marcelomaximiano/BoardGame/boardgame.jpg

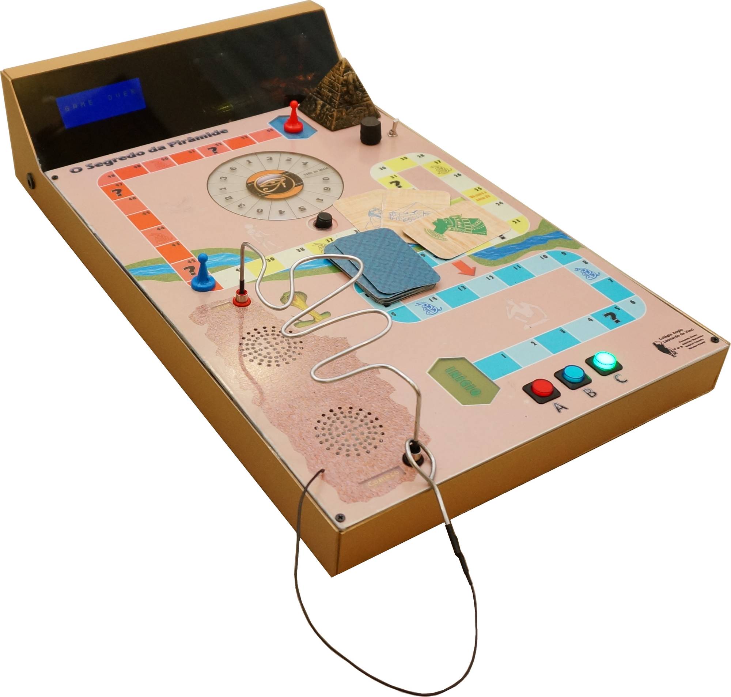
boardgame.jpg
