marcelomaximiano/BoardGame/hardware/BoardGame_pcb.png

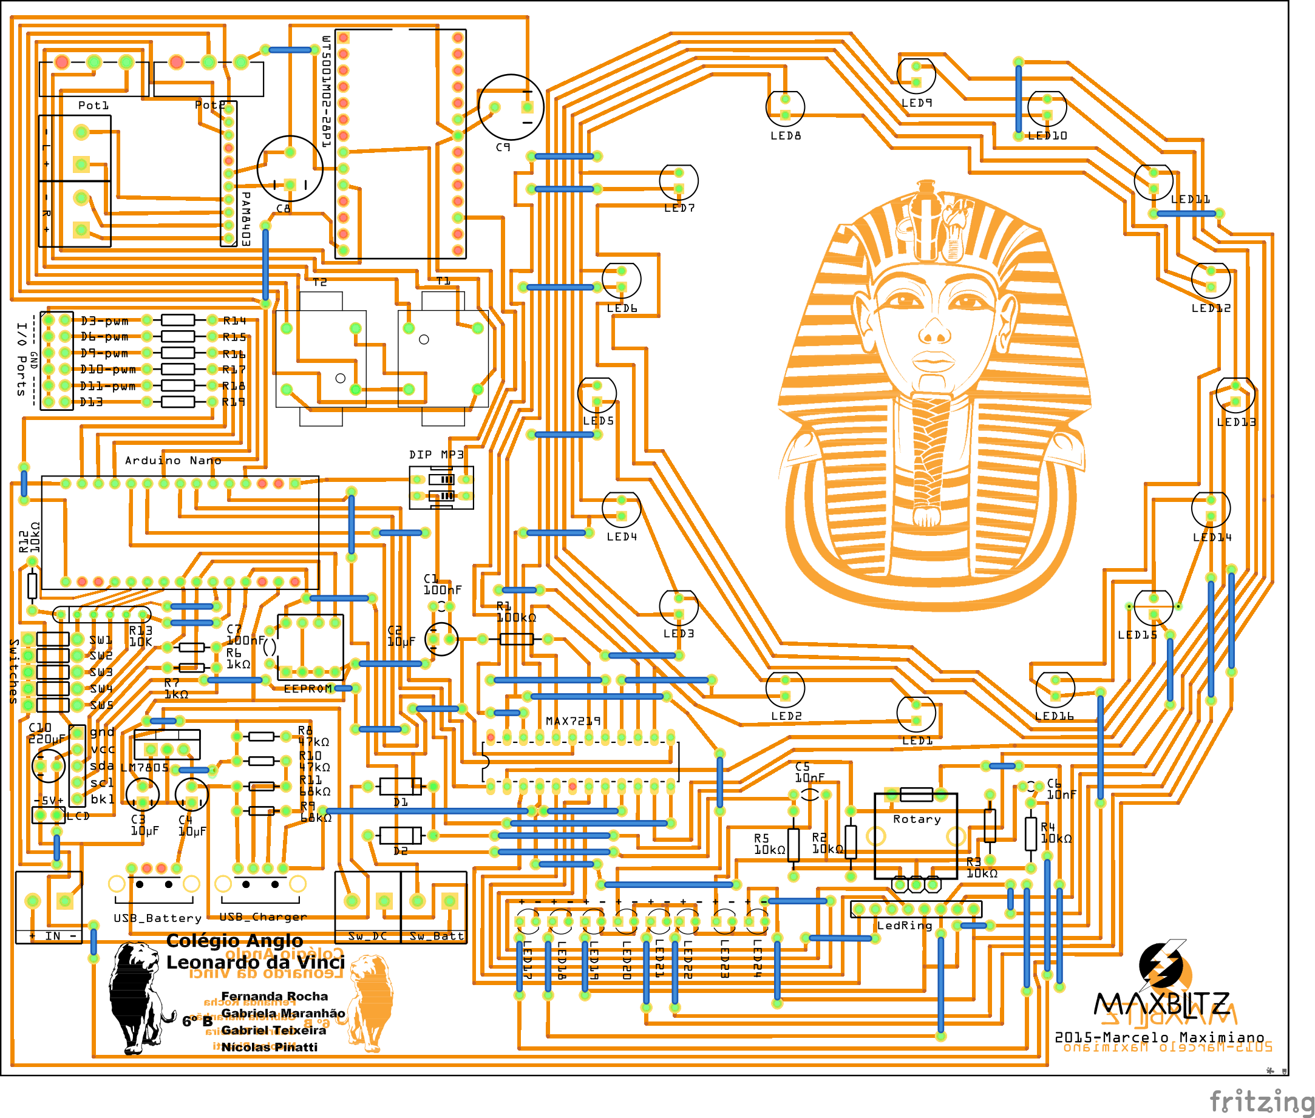
hardware/BoardGame_pcb.png
