marcelomaximiano/BoardGame/pictures/01-Board_sketch.jpg

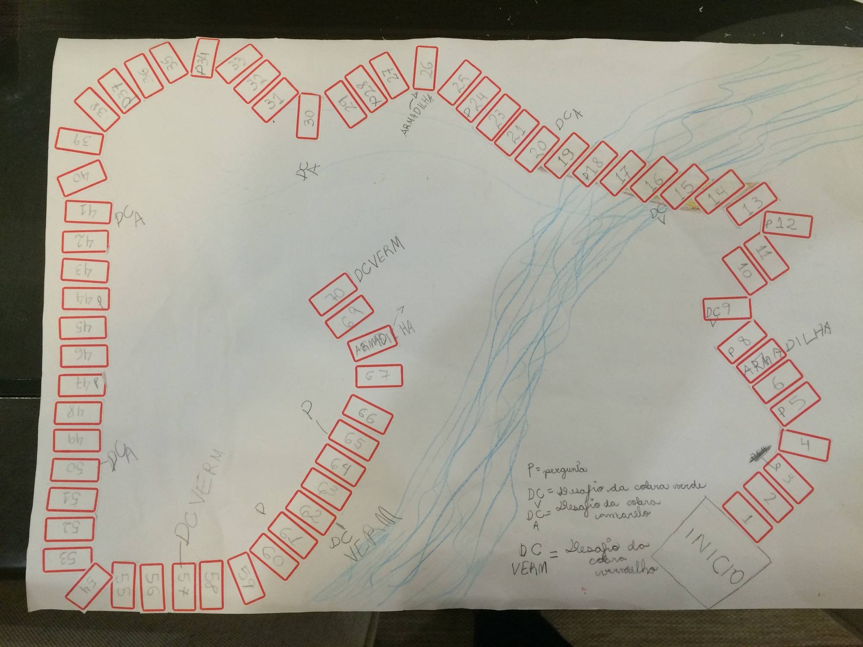
pictures/01-Board_sketch.jpg
