marcelomaximiano/BoardGame/pictures/02-First_Prototype.jpg

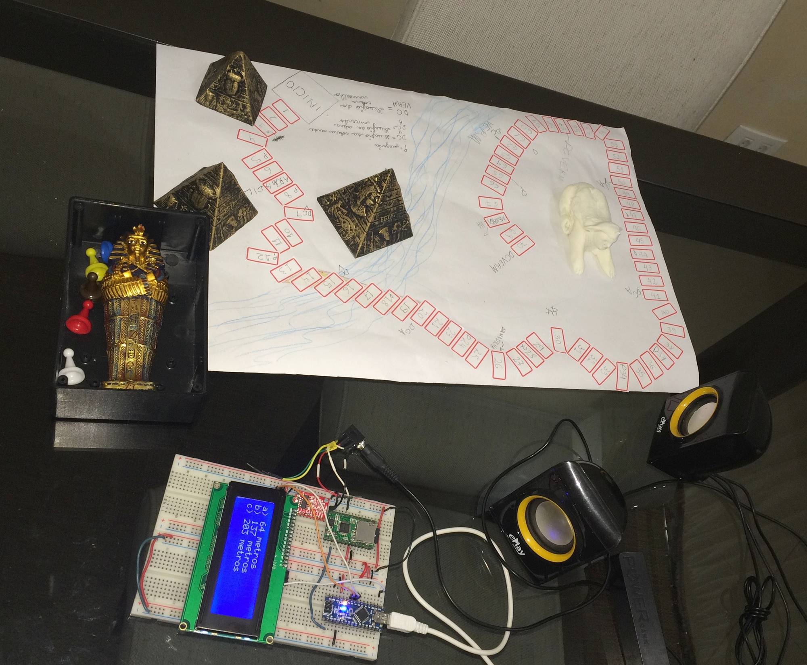
pictures/02-First_Prototype.jpg
