marcelomaximiano/BoardGame/pictures/03-PCB_tone_transfer.jpg

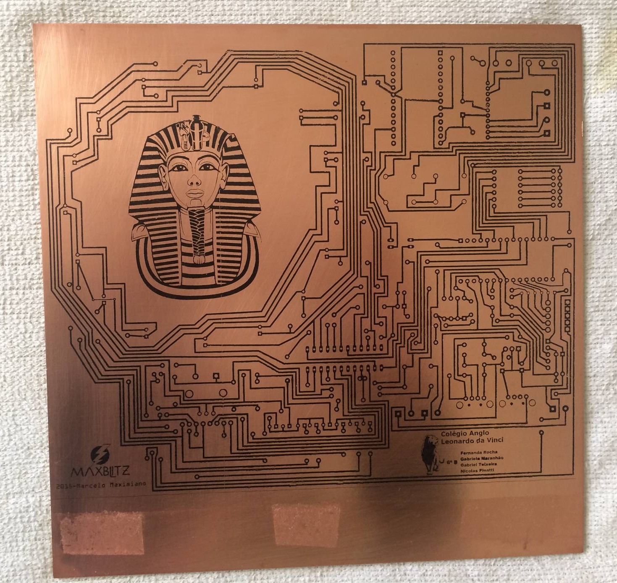
pictures/03-PCB_tone_transfer.jpg
