marcelomaximiano/BoardGame/pictures/04-PCB_Etched.jpg

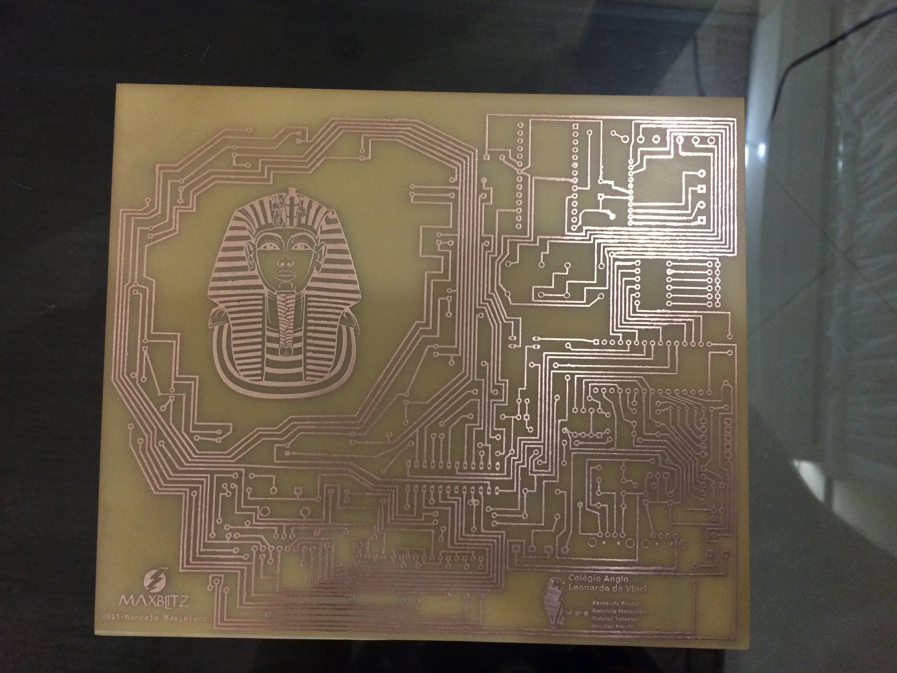
pictures/04-PCB_Etched.jpg
