marcelomaximiano/BoardGame/pictures/08-PCB_ready.jpg

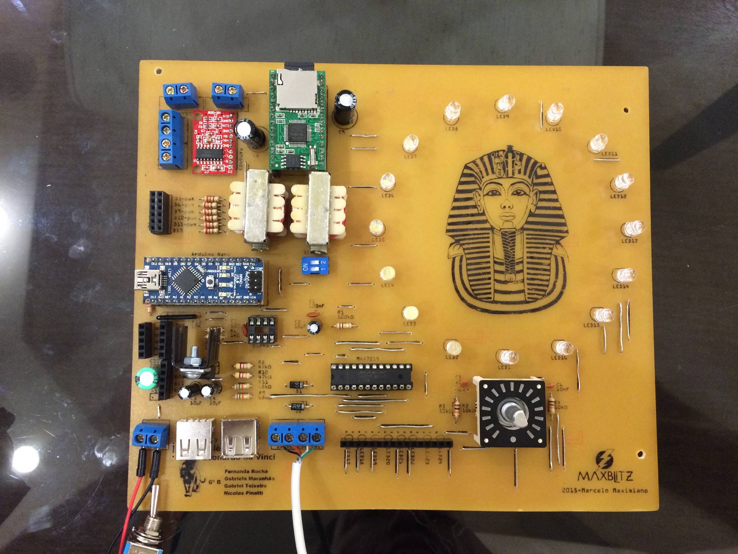
pictures/08-PCB_ready.jpg
