marcelomaximiano/BoardGame/pictures/12-Enclosure_cutting.jpg

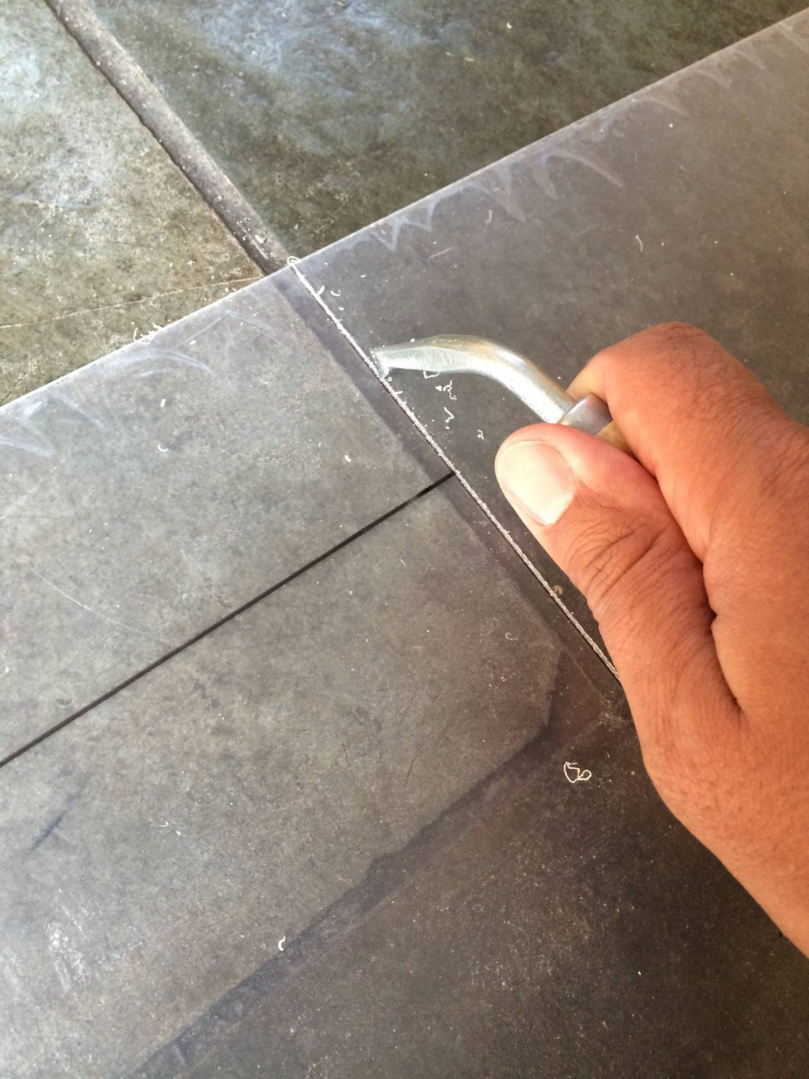
pictures/12-Enclosure_cutting.jpg
