marcelomaximiano/BoardGame/pictures/13-Enclosure_glueing.jpg

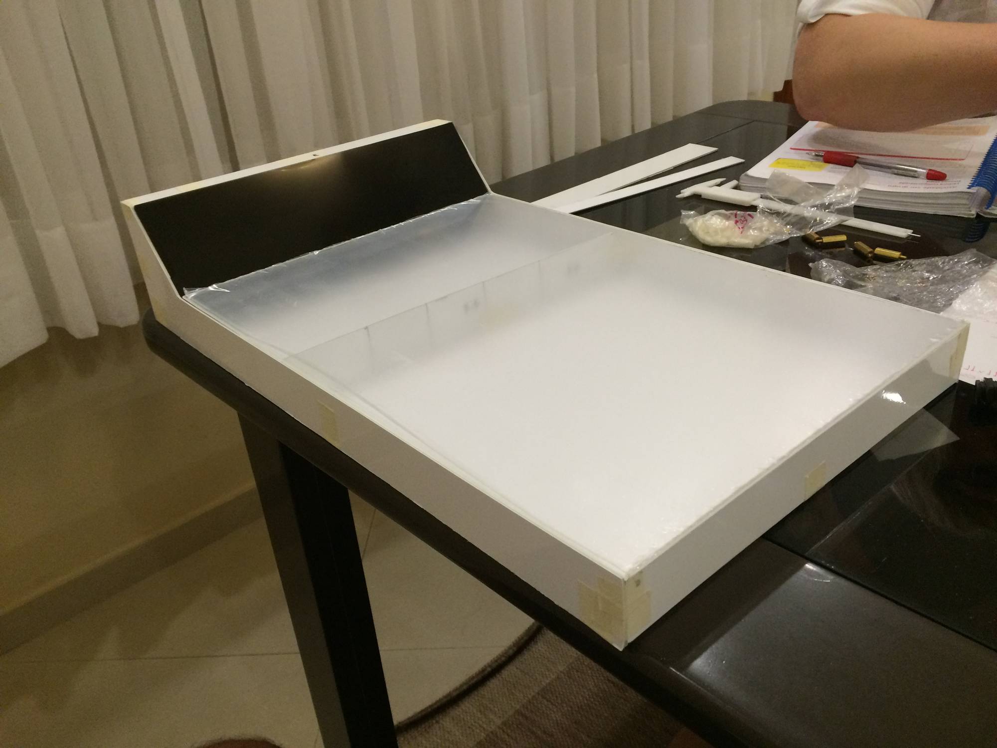
pictures/13-Enclosure_glueing.jpg
