marcelomaximiano/BoardGame/pictures/14-Enclosure_paint_prepation.jpg

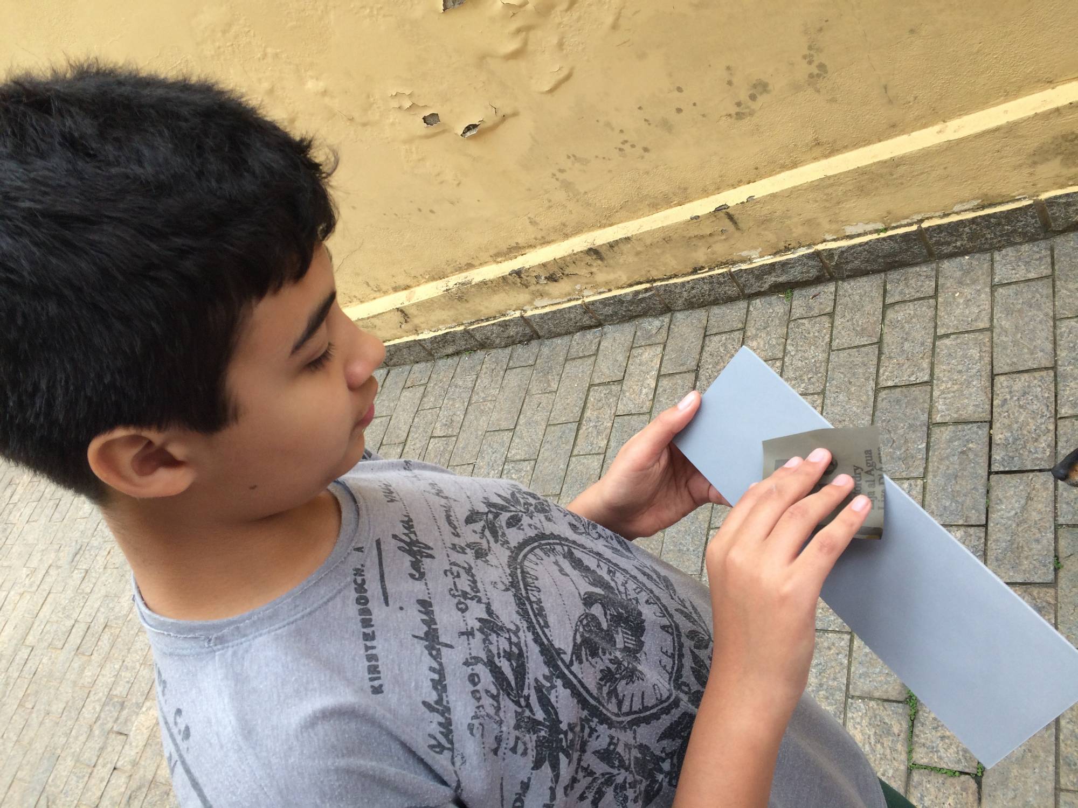
pictures/14-Enclosure_paint_prepation.jpg
