marcelomaximiano/BoardGame/pictures/15-Enclosure_paint_preparation2.jpg

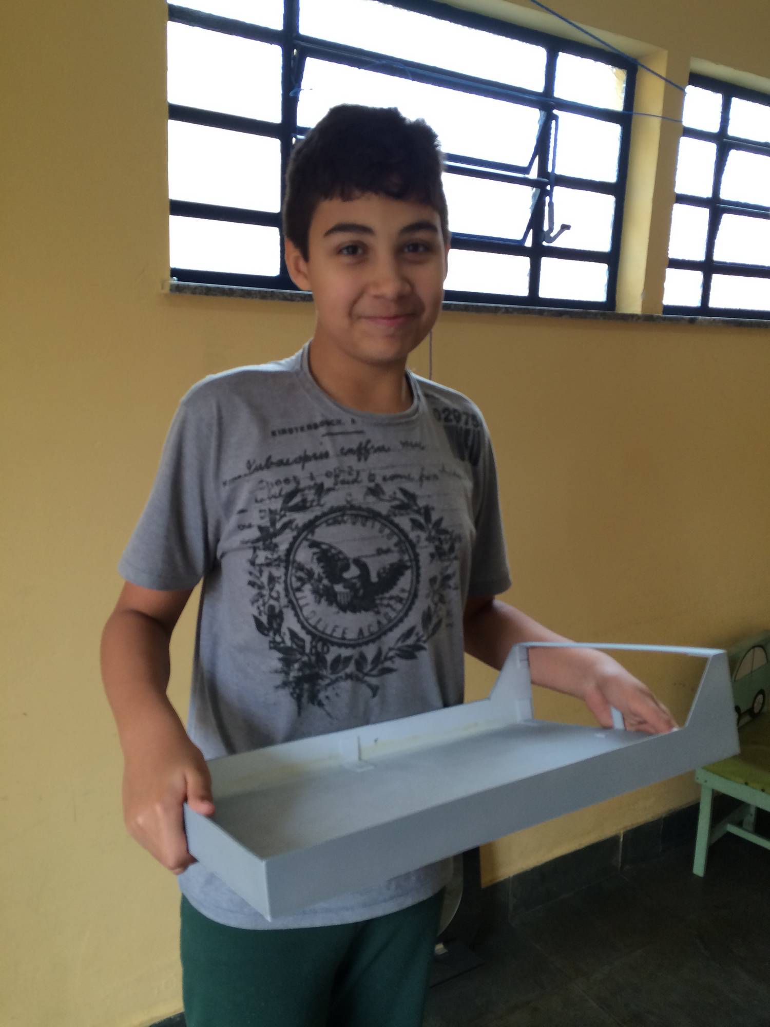
pictures/15-Enclosure_paint_preparation2.jpg
