marcelomaximiano/BoardGame/pictures/16-Enclosure_painting.jpg

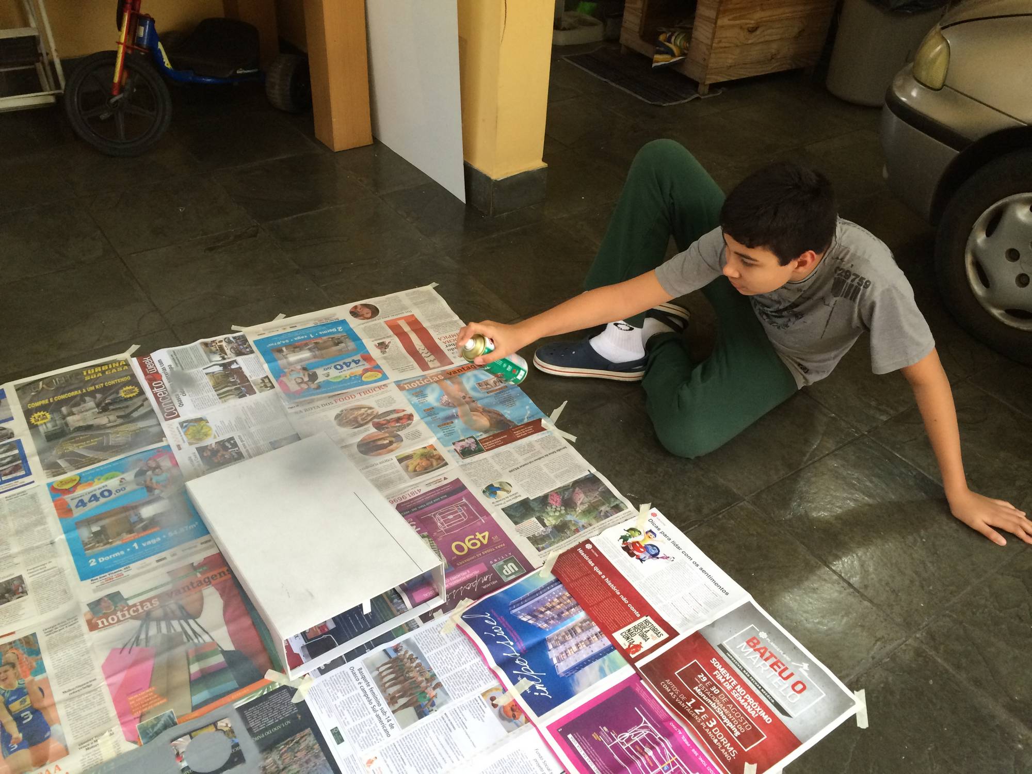
pictures/16-Enclosure_painting.jpg
