marcelomaximiano/BoardGame/pictures/18-Voice_recording.jpg

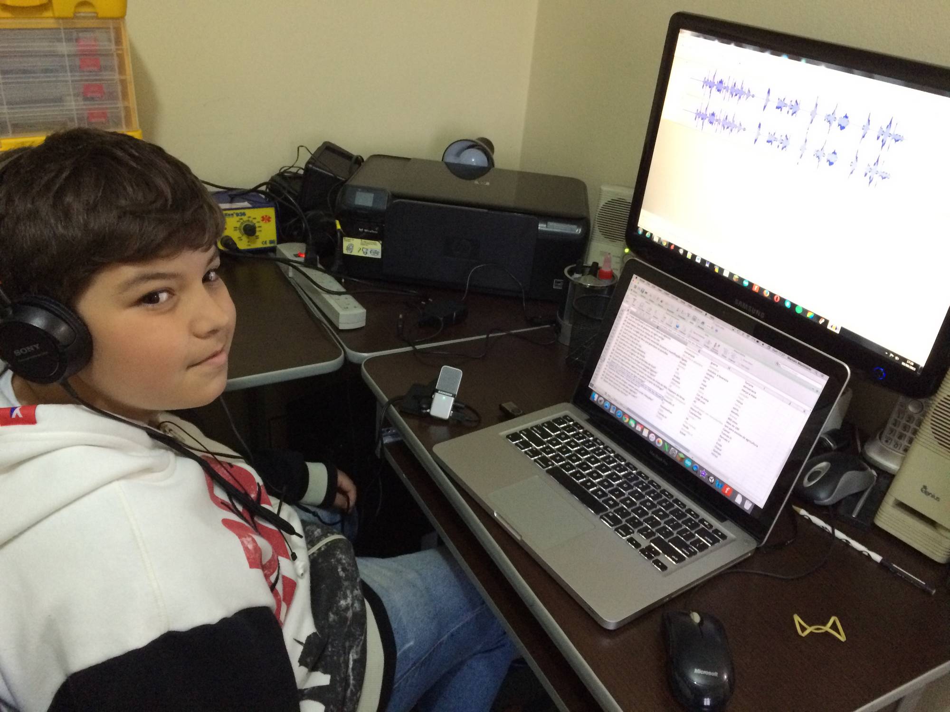
pictures/18-Voice_recording.jpg
