marcelomaximiano/BoardGame/pictures/20-RedPlayerWon_Secret_Revealed.jpg

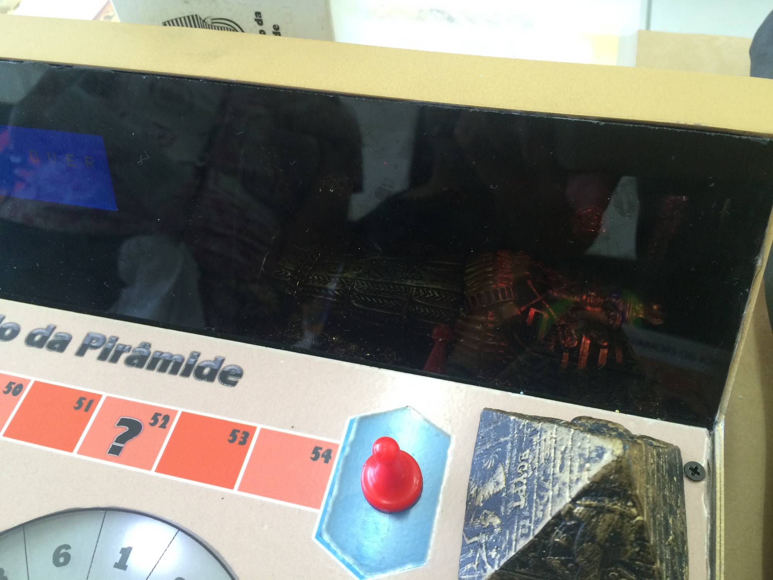
pictures/20-RedPlayerWon_Secret_Revealed.jpg
