marcelomaximiano/BoardGame/pictures/21-Pharaoh_Revealed.jpg

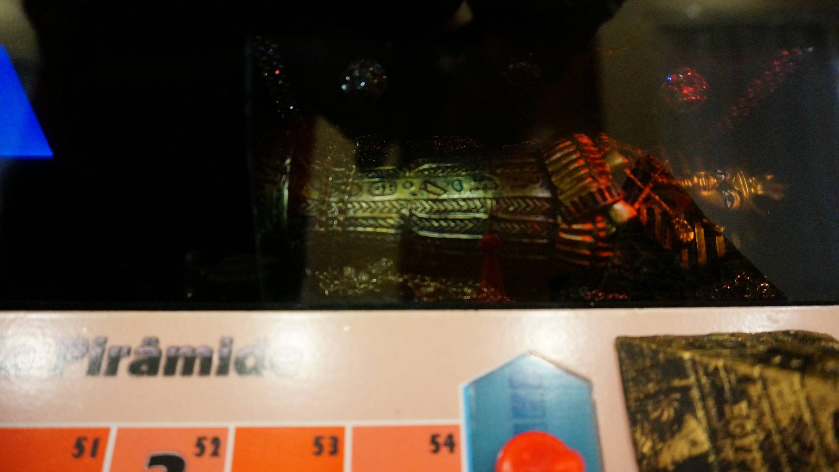
pictures/21-Pharaoh_Revealed.jpg
