marcelomaximiano/BoardGame/pictures/06-Nick_Soldering2.jpg

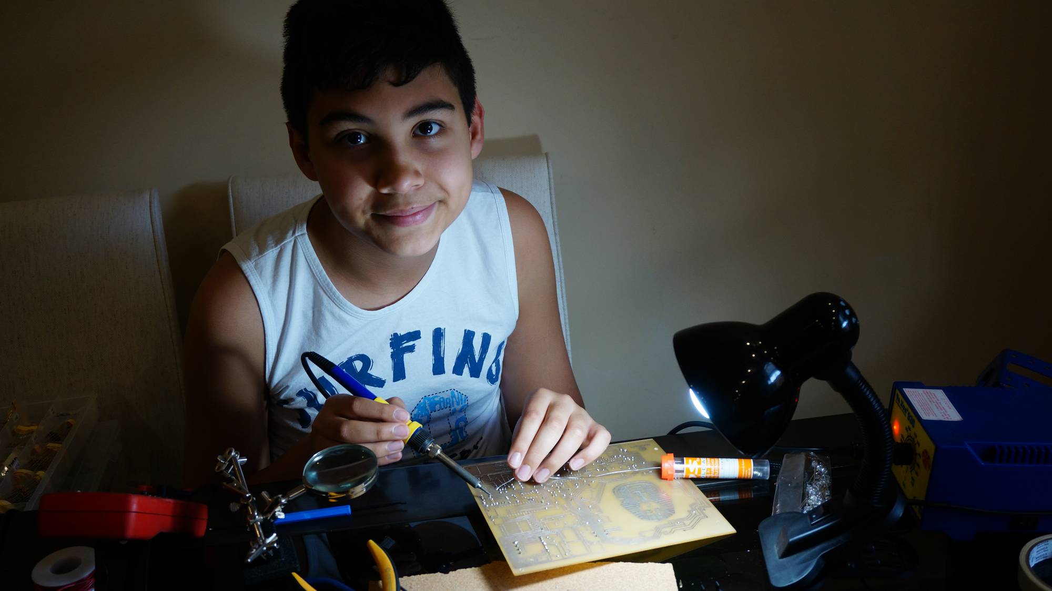
pictures/06-Nick_Soldering2.jpg
