marcelomaximiano/BoardGame/pictures/07-PCB-Soldered.jpg

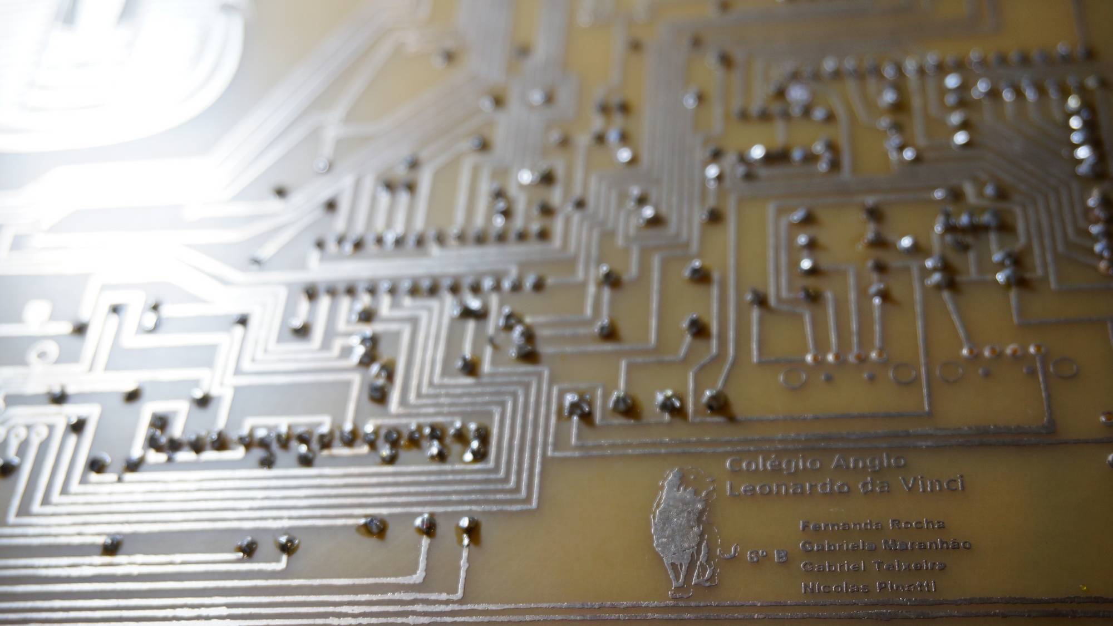
pictures/07-PCB-Soldered.jpg
