marcelomaximiano/BoardGame/pictures/09-PCB_testing.jpg

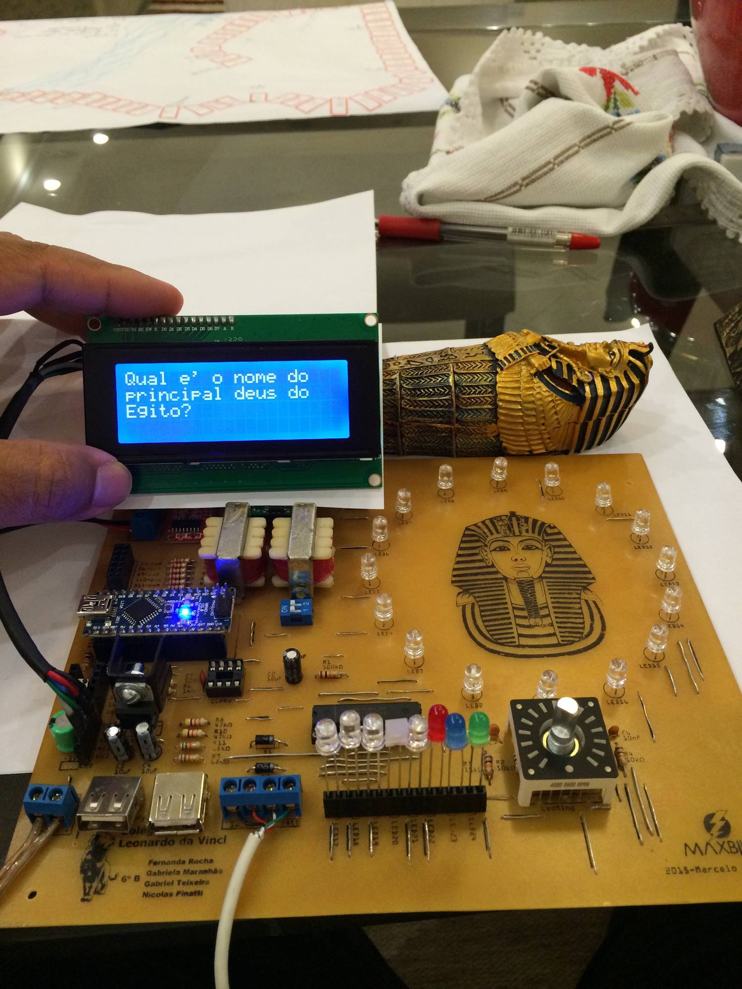
pictures/09-PCB_testing.jpg
